costarc/msxcart_flash32k/hardware/msx_eeprom.kicad_sch

## KiCad design hardware/msx_eeprom.kicad_sch (2024-05-20)

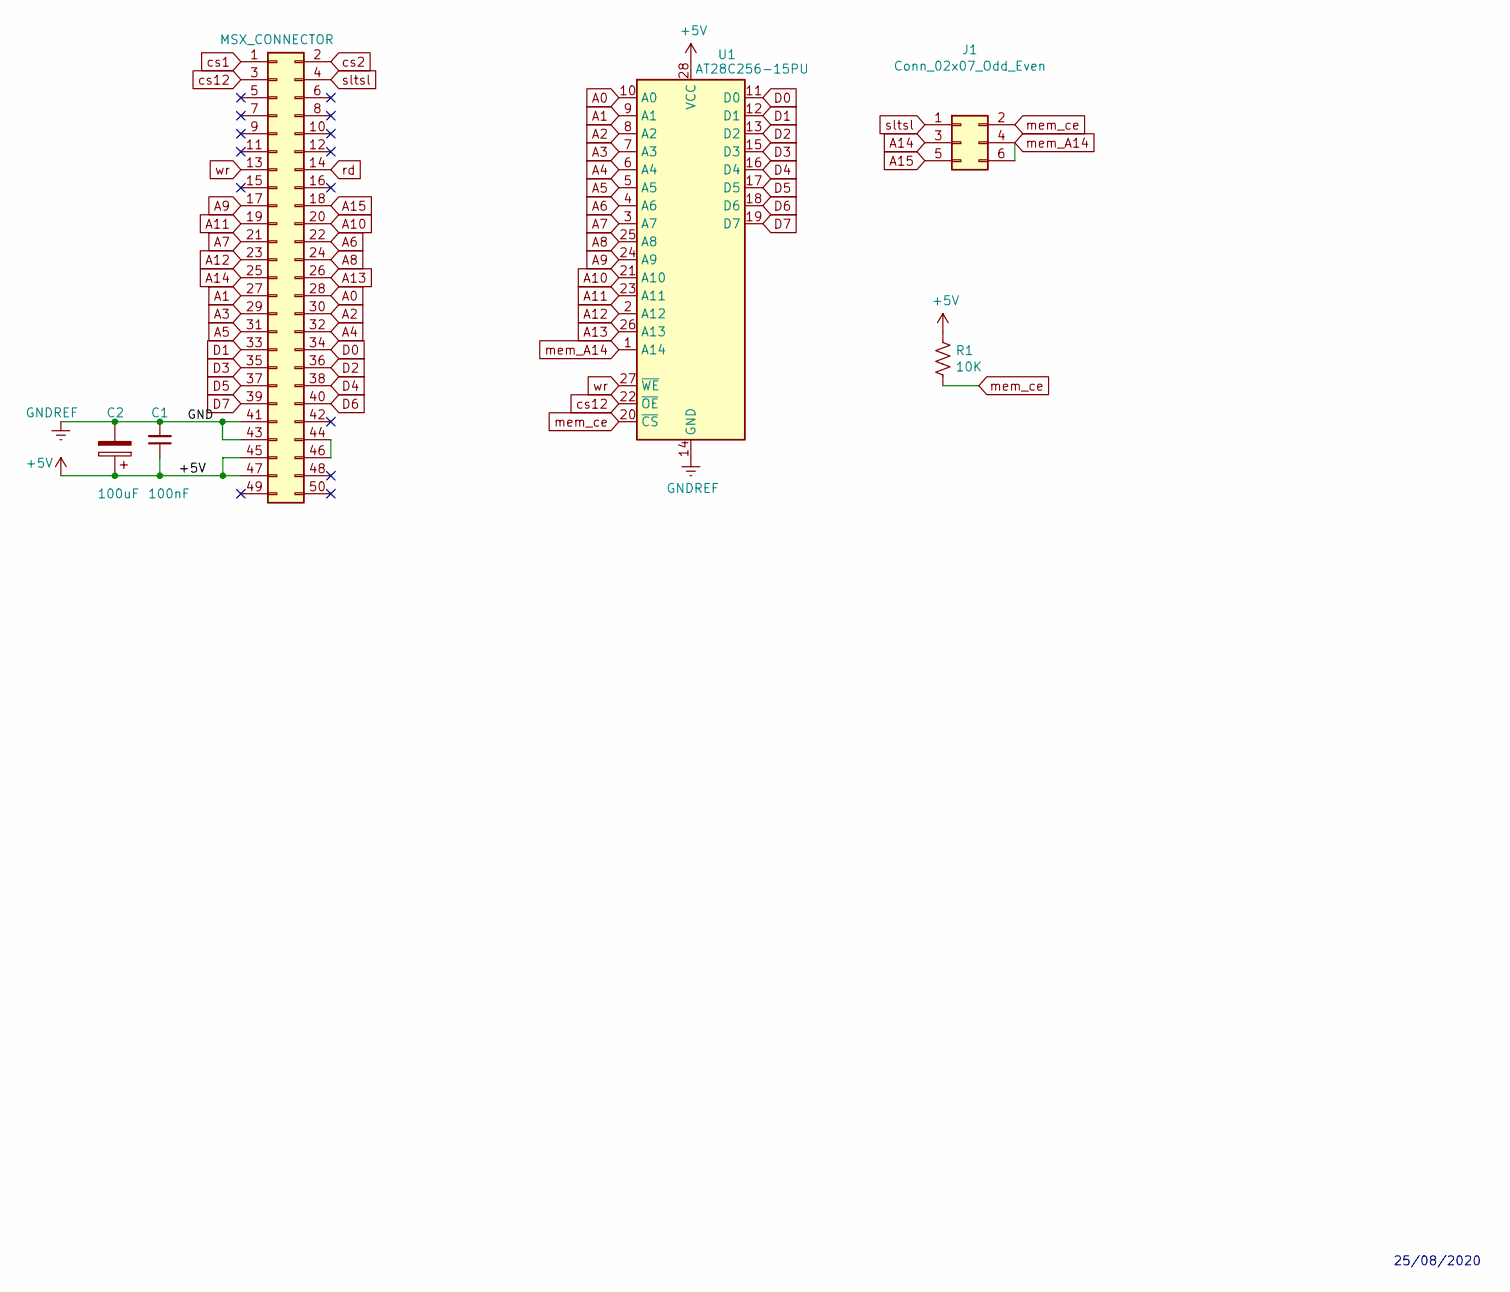
[picture p3: schematic msx_eeprom.kicad_sch]

Parts:
C1: 100nF; C_Disc_D3.0mm_W1.6mm_P2.50mm
C2: 100uF; CP_Radial_D5.0mm_P2.50mm
J1: Conn_02x07_Odd_Even; PinHeader_2x03_P2.54mm_Horizontal
P1: MSX_CONNECTOR; MSX_CART_SW_Official_3Holes
R1: 10K; R_Axial_DIN0207_L6.3mm_D2.5mm_P7.62mm_Horizontal
U1: AT28C256-15PU; DIP254P1524X482-28

Connections:
+5V: C1.1, C2.1, P1.45, P1.47, R1.1, U1.28 (VCC)
A0: P1.28, U1.10 (A0)
A1: P1.27, U1.9 (A1)
A2: P1.30, U1.8 (A2)
A3: P1.29, U1.7 (A3)
A4: P1.32, U1.6 (A4)
A5: P1.31, U1.5 (A5)
A6: P1.22, U1.4 (A6)
A7: P1.21, U1.3 (A7)
A8: P1.24, U1.25 (A8)
A9: P1.17, U1.24 (A9)
A10: P1.20, U1.21 (A10)
A11: P1.19, U1.23 (A11)
A12: P1.23, U1.2 (A12)
A13: P1.26, U1.26 (A13)
A14: J1.3, P1.25
A15: J1.5, P1.18
D0: P1.34, U1.11 (D0)
D1: P1.33, U1.12 (D1)
D2: P1.36, U1.13 (D2)
D3: P1.35, U1.15 (D3)
D4: P1.38, U1.16 (D4)
D5: P1.37, U1.17 (D5)
D6: P1.40, U1.18 (D6)
D7: P1.39, U1.19 (D7)
GNDREF: C1.2, C2.2, P1.41, P1.43, U1.14 (GND)
unnamed: P1.44, P1.46
cs1: P1.1
cs2: P1.2
cs12: P1.3, U1.22 (~OE)
mem_A14: J1.4, J1.6, U1.1 (A14)
mem_ce: J1.2, R1.2, U1.20 (~CS)
rd: P1.14
sltsl: J1.1, P1.4
wr: P1.13, U1.27 (~WE)

Notes on the sheet:
25/08/2020
